JessicaQiu0/Team-17-Shoulder-Miniproject/hardware/electrical/Electrical_Schematic.kicad_sch

## KiCad design hardware/electrical/Electrical_Schematic.kicad_sch (2026-09-11)

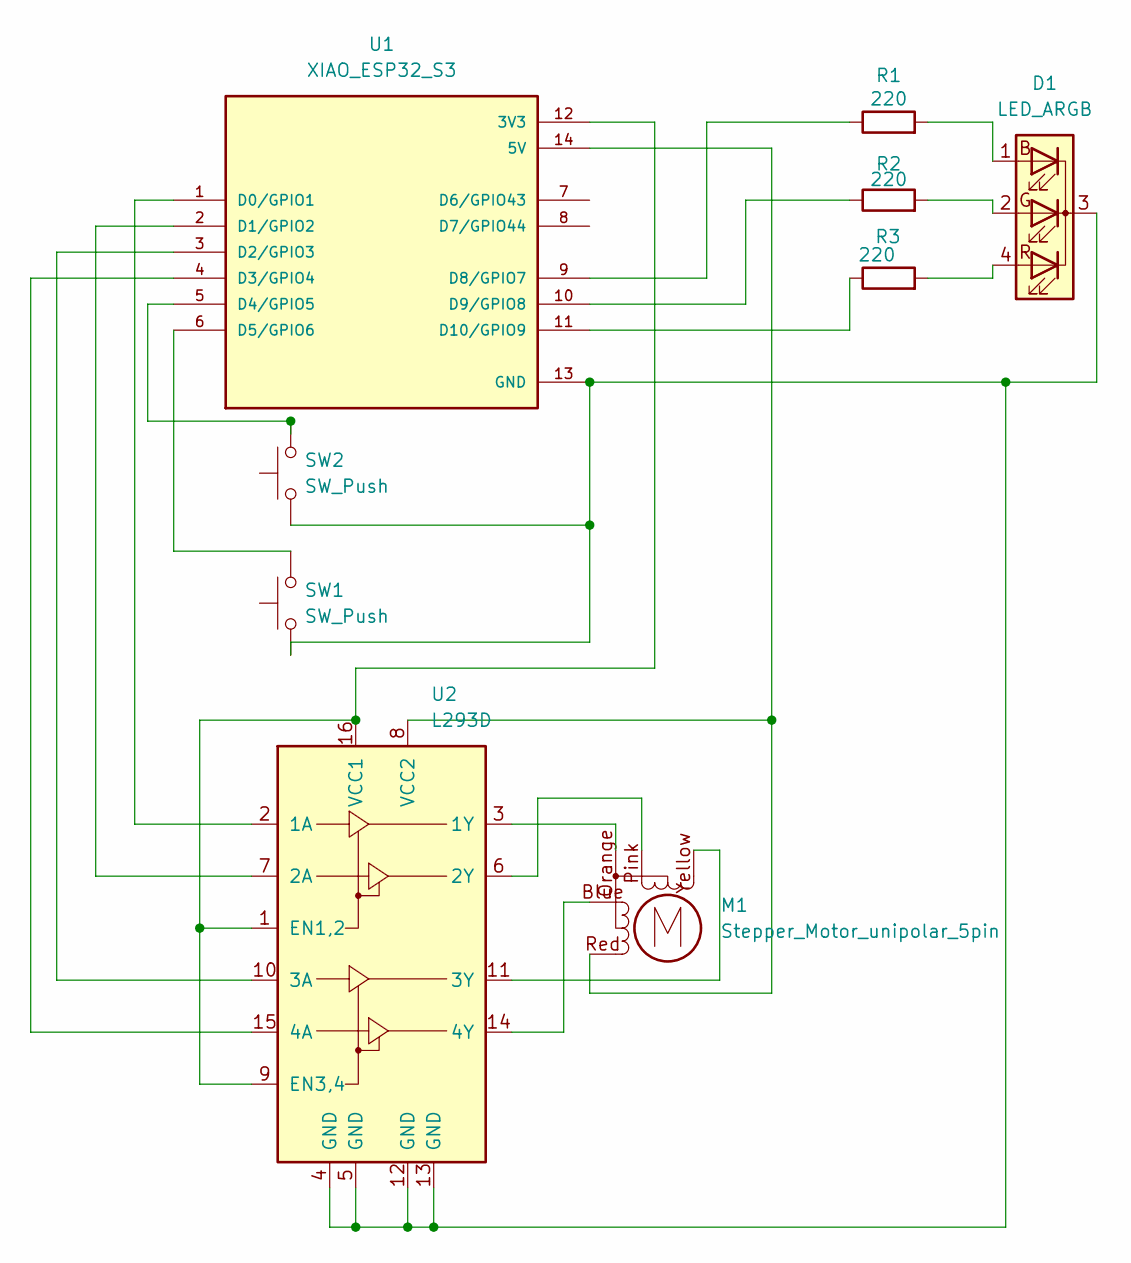
[picture p10: schematic Electrical_Schematic.kicad_sch]

Parts:
D1: LED_ARGB
M1: Stepper_Motor_unipolar_5pin
R1, R2, R3: 220
SW1, SW2: SW_Push
U1: XIAO_ESP32_S3; MODULE_XIAO_ESP32_S3; PARTREV April 22nd, 2026
U2: L293D; DIP-16_W7.62mm

Connections:
unnamed: D1.1 (BA), R1.2
unnamed: D1.2 (GA), R2.2
unnamed: D1.3 (K), SW1.1, SW2.1, U1.13 (GND), U2.4 (GND), U2.5 (GND), U2.12 (GND), U2.13 (GND)
unnamed: D1.4 (RA), R3.2
unnamed: M1.Blue, U2.14 (4Y)
unnamed: M1.Orange, U2.3 (1Y)
unnamed: M1.Pink, U2.6 (2Y)
unnamed: M1.Red, U1.14 (5V), U2.8 (VCC2)
unnamed: M1.Yellow, U2.11 (3Y)
unnamed: R1.1, U1.9 (D8/GPIO7)
unnamed: R2.1, U1.10 (D9/GPIO8)
unnamed: R3.1, U1.11 (D10/GPIO9)
unnamed: SW1.2, U1.6 (D5/GPIO6)
unnamed: SW2.2, U1.5 (D4/GPIO5)
unnamed: U1.1 (D0/GPIO1), U2.2 (1A)
unnamed: U1.2 (D1/GPIO2), U2.7 (2A)
unnamed: U1.3 (D2/GPIO3), U2.10 (3A)
unnamed: U1.4 (D3/GPIO4), U2.15 (4A)
unnamed: U1.12 (3V3), U2.1 (EN1,2), U2.9 (EN3,4), U2.16 (VCC1)
